ZhengNan6/stm32f103c8t6_oled/stm32_code/OLED/bmp.h

//////////////////////////////////////////////////////////////////////////////////	 
//本程序只供学习使用，未经作者许可，不得用于其它任何用途
//测试硬件：单片机STM32F103RCT6,正点原子MiniSTM32开发板,主频72MHZ，晶振12MHZ
//QDtech-OLED液晶驱动 for STM32
//xiao冯@ShenZhen QDtech co.,LTD
//公司网站:www.qdtft.com
//淘宝网站：http://qdtech.taobao.com
//wiki技术网站：http://www.lcdwiki.com
//我司提供技术支持，任何技术问题欢迎随时交流学习
//固话(传真) :+86 0755-23594567 
//手机:15989313508（冯工） 
//邮箱:lcdwiki01@gmail.com    support@lcdwiki.com    goodtft@163.com
//技术支持QQ:3002773612  3002778157
//技术交流QQ群:324828016
//创建日期:2018/8/27
//版本：V1.0
//版权所有，盗版必究。
//Copyright(C) 深圳市全动电子技术有限公司 2018-2028
//All rights reserved
/****************************************************************************************************
//=========================================电源接线================================================//
// OLED模块               STM32单片机
//   VCC         接       DC 5V/3.3V      //OLED屏电源正
//   GND         接          GND          //OLED屏电源地
//=======================================液晶屏数据线接线==========================================//
//本模块默认数据总线类型为4线制SPI
// OLED模块               STM32单片机
//   D1          接          PB15        //OLED屏SPI写信号
//=======================================液晶屏控制线接线==========================================//
// OLED模块               STM32单片机
//   CS          接          PB11        //OLED屏片选控制信号
//   RES         接          PB12        //OLED屏复位控制信号
//   DC          接          PB10        //OLED屏数据/命令选择控制信号
//   D0          接          PB13        //OLED屏SPI时钟信号
//=========================================触摸屏接线=========================================//
//本模块不带触摸功能，所以不需要触摸屏接线
****************************************************************************************************/	
/***************************************************************************************************
  * @attention
  *
  * THE PRESENT FIRMWARE WHICH IS FOR GUIDANCE ONLY AIMS AT PROVIDING CUSTOMERS
  * WITH CODING INFORMATION REGARDING THEIR PRODUCTS IN ORDER FOR THEM TO SAVE
  * TIME. AS A RESULT, QD electronic SHALL NOT BE HELD LIABLE FOR ANY
  * DIRECT, INDIRECT OR CONSEQUENTIAL DAMAGES WITH RESPECT TO ANY CLAIMS ARISING
  * FROM THE CONTENT OF SUCH FIRMWARE AND/OR THE USE MADE BY CUSTOMERS OF THE
  * CODING INFORMATION CONTAINED HEREIN IN CONNECTION WITH THEIR PRODUCTS.
****************************************************************************************************/
//////////////////////////////////////////////////////////////////////////////////	 
//
//存储图片数据，图片大小为128*64像素
//逐行式，顺向（高位在前）
//
/////////////////////////////////////////////////////////////////////////////////

#ifndef __BMP_H
#define __BMP_H

unsigned char BMP2[] =
{
	0x00,0x00,0x00,0x00,0x00,0x00,0x00,0x00,0x00,0x00,0x00,0x00,0x00,0x00,0x00,0x00,
	0x7F,0xE0,0x03,0x91,0x1C,0x38,0x18,0x00,0x70,0x00,0xFF,0xFC,0x00,0x07,0xFF,0xFE,
	0x66,0x60,0x04,0x5B,0x22,0x44,0x14,0x01,0x8C,0x01,0x7F,0xFA,0x00,0x04,0x00,0x02,
	0x36,0xC0,0x08,0x15,0x40,0x80,0x52,0x02,0x02,0x01,0xBF,0xF6,0x00,0x3D,0xB6,0xDA,
	0x1F,0x80,0x88,0x11,0x40,0x80,0x34,0x04,0x71,0x01,0xDF,0xEE,0x00,0x25,0xB6,0xDA,
	0x0F,0x02,0x88,0x11,0x40,0x80,0x18,0x00,0x88,0x01,0xE0,0x1E,0x00,0x25,0xB6,0xDA,
	0x06,0x0A,0x88,0x11,0x40,0x80,0x34,0x01,0x04,0x01,0xDF,0xEE,0x00,0x25,0xB6,0xDA,
	0x06,0x2A,0x88,0x11,0x40,0x80,0x52,0x00,0x20,0x01,0xBF,0xF6,0x00,0x3D,0xB6,0xDA,
	0x06,0xAA,0x84,0x51,0x22,0x44,0x14,0x00,0x70,0x01,0x7F,0xFA,0x00,0x04,0x00,0x02,
	0x06,0xAA,0x83,0x91,0x1C,0x38,0x18,0x00,0x20,0x00,0xFF,0xFC,0x00,0x07,0xFF,0xFE,
	0x00,0x00,0x00,0x00,0x00,0x00,0x00,0x00,0x00,0x00,0x00,0x00,0x00,0x00,0x00,0x00,
	0x00,0x00,0x00,0x00,0x00,0x00,0x00,0x00,0x00,0x00,0x00,0x00,0x00,0x00,0x00,0x00,
	0x00,0x00,0x00,0x00,0x00,0x00,0x00,0x00,0x00,0x00,0x00,0x00,0x00,0x00,0x00,0x00,
	0x00,0x00,0x00,0x00,0x00,0x00,0x00,0x00,0x00,0x00,0x00,0x00,0x00,0x00,0x00,0x00,
	0x00,0x00,0x00,0x00,0x00,0x00,0x00,0x00,0x00,0x00,0x00,0x00,0x00,0x00,0x00,0x00,
	0x00,0x00,0x00,0x00,0x00,0x00,0x00,0x00,0x00,0x00,0x00,0x00,0x00,0x00,0x00,0x00,
	0x00,0x00,0x00,0x00,0x03,0x1F,0xFC,0x00,0x3F,0xFC,0x7F,0xF0,0x00,0x00,0x00,0x00,
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
	0x00,0x00,0x00,0x00,0x07,0x80,0x3E,0x00,0x00,0x00,0x00,0x3F,0x80,0x0F,0xE1,0xC0,
	0x00,0x1F,0xFC,0x00,0x03,0xFF,0xFC,0x03,0xFF,0xF0,0x00,0x00,0xFF,0xFF,0xFF,0xFF,
	0x00,0x00,0x00,0x00,0xFF,0xFF,0x80,0x00,0x00,0x00,0x00,0x01,0xFC,0x00,0x00,0x00,
};
#endif
