ZhengNan6/stm32f103c8t6_oled/stm32_code/OLED/oledfont.h

//////////////////////////////////////////////////////////////////////////////////	 
//本程序只供学习使用，未经作者许可，不得用于其它任何用途
//测试硬件：单片机STM32F103RCT6,正点原子MiniSTM32开发板,主频72MHZ，晶振12MHZ
//QDtech-OLED液晶驱动 for STM32
//xiao冯@ShenZhen QDtech co.,LTD
//公司网站:www.qdtft.com
//淘宝网站：http://qdtech.taobao.com
//wiki技术网站：http://www.lcdwiki.com
//我司提供技术支持，任何技术问题欢迎随时交流学习
//固话(传真) :+86 0755-23594567 
//手机:15989313508（冯工） 
//邮箱:lcdwiki01@gmail.com    support@lcdwiki.com    goodtft@163.com
//技术支持QQ:3002773612  3002778157
//技术交流QQ群:324828016
//创建日期:2018/8/27
//版本：V1.0
//版权所有，盗版必究。
//Copyright(C) 深圳市全动电子技术有限公司 2018-2028
//All rights reserved
/****************************************************************************************************
//=========================================电源接线================================================//
// OLED模块               STM32单片机
//   VCC         接       DC 5V/3.3V      //OLED屏电源正
//   GND         接          GND          //OLED屏电源地
//=======================================液晶屏数据线接线==========================================//
//本模块默认数据总线类型为4线制SPI
// OLED模块               STM32单片机
//   D1          接          PB15        //OLED屏SPI写信号
//=======================================液晶屏控制线接线==========================================//
// OLED模块               STM32单片机
//   CS          接          PB11        //OLED屏片选控制信号
//   RES         接          PB12        //OLED屏复位控制信号
//   DC          接          PB10        //OLED屏数据/命令选择控制信号
//   D0          接          PB13        //OLED屏SPI时钟信号
//=========================================触摸屏接线=========================================//
//本模块不带触摸功能，所以不需要触摸屏接线
****************************************************************************************************/	
/***************************************************************************************************
  * @attention
  *
  * THE PRESENT FIRMWARE WHICH IS FOR GUIDANCE ONLY AIMS AT PROVIDING CUSTOMERS
  * WITH CODING INFORMATION REGARDING THEIR PRODUCTS IN ORDER FOR THEM TO SAVE
  * TIME. AS A RESULT, QD electronic SHALL NOT BE HELD LIABLE FOR ANY
  * DIRECT, INDIRECT OR CONSEQUENTIAL DAMAGES WITH RESPECT TO ANY CLAIMS ARISING
  * FROM THE CONTENT OF SUCH FIRMWARE AND/OR THE USE MADE BY CUSTOMERS OF THE
  * CODING INFORMATION CONTAINED HEREIN IN CONNECTION WITH THEIR PRODUCTS.
****************************************************************************************************/	
#ifndef __OLEDFONT_H
#define __OLEDFONT_H 	   
//常用ASCII表
//偏移量32
//ASCII字符集
//偏移量32
//大小:6*8
//逐行式，顺向（高位在前）
/************************************6*8的点阵************************************/
const unsigned char F6x8[][8] =		
{
	0x00,0x00,0x00,0x00,0x00,0x00,0x00,0x00, // sp
	0x10,0x10,0x10,0x10,0x00,0x10,0x00,0x00, // !
	0x28,0x28,0x28,0x00,0x00,0x00,0x00,0x00, // "
	0x28,0x28,0x7C,0x28,0x7C,0x28,0x28,0x00, // #
	0x10,0x3C,0x50,0x38,0x14,0x78,0x10,0x00, // $
	0x00,0x4C,0x2C,0x10,0x08,0x60,0x60,0x00, // %
	0x30,0x48,0x50,0x20,0x54,0x48,0x34,0x00, // &
	0x30,0x10,0x20,0x00,0x00,0x00,0x00,0x00, // '
	0x08,0x10,0x20,0x20,0x20,0x10,0x08,0x00, // (
	0x20,0x10,0x08,0x08,0x08,0x10,0x20,0x00, // )
	0x00,0x10,0x54,0x38,0x54,0x10,0x00,0x00, // *
	0x00,0x10,0x10,0x7C,0x10,0x10,0x00,0x00, // +
	0x00,0x00,0x00,0x00,0x00,0x18,0x08,0x10, // ,
	0x00,0x00,0x00,0x00,0x7C,0x00,0x00,0x00, // -
	0x00,0x00,0x00,0x00,0x00,0x30,0x30,0x00, // .
	0x00,0x04,0x08,0x10,0x20,0x40,0x00,0x00, // /
	0x38,0x44,0x4C,0x54,0x64,0x44,0x38,0x00, // 0
	0x10,0x30,0x10,0x10,0x10,0x10,0x38,0x00, // 1
	0x38,0x44,0x04,0x08,0x10,0x20,0x7C,0x00, // 2
	0x7C,0x08,0x10,0x08,0x04,0x44,0x38,0x00, // 3 
	0x08,0x18,0x28,0x48,0x7C,0x08,0x08,0x00, // 4
	0x7C,0x40,0x78,0x04,0x04,0x44,0x38,0x00, // 5
	0x18,0x20,0x40,0x78,0x44,0x44,0x38,0x00, // 6
	0x7C,0x04,0x08,0x10,0x20,0x20,0x20,0x00, // 7
	0x38,0x44,0x44,0x38,0x44,0x44,0x38,0x00, // 8
	0x38,0x44,0x44,0x3C,0x04,0x08,0x30,0x00, // 9
	0x00,0x30,0x30,0x00,0x30,0x30,0x00,0x00, // :
	0x00,0x30,0x30,0x00,0x30,0x10,0x20,0x00, // ;
	0x08,0x10,0x20,0x40,0x20,0x10,0x08,0x00, // <
	0x00,0x00,0x7C,0x00,0x7C,0x00,0x00,0x00, // =
	0x20,0x10,0x08,0x04,0x08,0x10,0x20,0x00, // >
	0x38,0x44,0x04,0x08,0x10,0x00,0x10,0x00, // ?
	0x38,0x44,0x04,0x34,0x5C,0x44,0x38,0x00, // @
	0x10,0x28,0x44,0x44,0x7C,0x44,0x44,0x00, // A
	0x78,0x44,0x44,0x78,0x44,0x44,0x78,0x00, // B
	0x38,0x44,0x40,0x40,0x40,0x44,0x38,0x00, // C
	0x70,0x48,0x44,0x44,0x44,0x48,0x70,0x00, // D
	0x7C,0x40,0x40,0x78,0x40,0x40,0x7C,0x00, // E
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
	"技",0x00,0x00,0x00,0x00,0x00,0x00,0x00,0x00,0x01,0x80,0x08,0x00,0x01,0xC0,0x0E,0x00,
	0x01,0x80,0x0C,0x00,0x01,0x80,0x0C,0x00,0x01,0x80,0x0C,0x00,0x01,0x80,0x0C,0x00,
	0x01,0x98,0x0C,0x18,0x3F,0xFF,0xFF,0xFC,0x01,0x80,0x0C,0x00,0x01,0x80,0x0C,0x00,
	0x01,0x80,0x0C,0x00,0x01,0x80,0x0C,0x00,0x01,0x8C,0x0C,0x20,0x01,0xB3,0xFF,0xF0,
	0x01,0xC0,0x80,0x60,0x0F,0x80,0x80,0x60,0x3D,0x80,0x40,0xC0,0x31,0x80,0x40,0xC0,
	0x01,0x80,0x21,0x80,0x01,0x80,0x21,0x80,0x01,0x80,0x33,0x00,0x01,0x80,0x1E,0x00,
	0x01,0x80,0x0C,0x00,0x01,0x80,0x1E,0x00,0x01,0x80,0x37,0x00,0x01,0x80,0xE3,0xC0,
	0x1F,0x83,0x80,0xF8,0x07,0x8E,0x00,0x7C,0x02,0x30,0x00,0x00,0x00,0x00,0x00,0x00,/*"技",4*/
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
};

#endif
